Thomas-Lawford/E-Reader-MINI/firmware/src/EPD/Display_EPD_W21_SPI.c

#include "Display_EPD_W21_spi.h"

//E-paper GPIO initialization
void EPD_GPIO_Init(void)
{
	    GPIO_InitTypeDef GPIO_InitStruct = {0};

    __HAL_RCC_GPIOA_CLK_ENABLE();
    __HAL_RCC_GPIOB_CLK_ENABLE();

    // CS (PA15), output
    GPIO_InitStruct.Pin = GPIO_PIN_15;
    GPIO_InitStruct.Mode = GPIO_MODE_OUTPUT_PP;
    GPIO_InitStruct.Pull = GPIO_NOPULL;
    GPIO_InitStruct.Speed = GPIO_SPEED_FREQ_LOW;
    HAL_GPIO_Init(GPIOA, &GPIO_InitStruct);

    // MOSI (PB5), CLK (PB3), DC (PB4), RST (PB6), output
    GPIO_InitStruct.Pin = GPIO_PIN_3 | GPIO_PIN_4 | GPIO_PIN_5 | GPIO_PIN_6;
    HAL_GPIO_Init(GPIOB, &GPIO_InitStruct);

    // BUSY (PB1), input with pull-up
    GPIO_InitStruct.Pin = GPIO_PIN_1;
    GPIO_InitStruct.Mode = GPIO_MODE_INPUT;
    GPIO_InitStruct.Pull = GPIO_PULLUP;
    HAL_GPIO_Init(GPIOB, &GPIO_InitStruct); //make sure configured in cubemx
}



//SPI write byte
void SPI_Write(unsigned char value)
{
	unsigned char i;
  EPD_W21_CLK_0;
	for(i=0;i<8;i++)
	{
		if(value&0x80)
		  EPD_W21_MOSI_1 ;
		else
		  EPD_W21_MOSI_0 ;
		EPD_W21_CLK_1;
	  EPD_W21_CLK_0;
		value=value<<1;
  }
}

//SPI write command
void EPD_W21_WriteCMD(unsigned char command)
{
	EPD_W21_CS_0;
	EPD_W21_DC_0;  // D/C#   0:command  1:data
	SPI_Write(command);
	EPD_W21_CS_1;
}
//SPI write data
void EPD_W21_WriteDATA(unsigned char datas)
{
	EPD_W21_CS_0;
	EPD_W21_DC_1;  // D/C#   0:command  1:data
	SPI_Write(datas);
	EPD_W21_CS_1;
}
