Thomas-Lawford/E-Reader-MINI/firmware/src/EPD/Display_EPD_W21_spi.h

#ifndef _DISPLAY_EPD_W21_SPI_
#define _DISPLAY_EPD_W21_SPI_
#include "stm32u0xx_hal.h"


#define EPD_W21_MOSI_0	HAL_GPIO_WritePin(GPIOB, GPIO_PIN_5, GPIO_PIN_RESET)
#define EPD_W21_MOSI_1	HAL_GPIO_WritePin(GPIOB, GPIO_PIN_5, GPIO_PIN_SET)

#define EPD_W21_CLK_0	HAL_GPIO_WritePin(GPIOB, GPIO_PIN_3, GPIO_PIN_RESET)
#define EPD_W21_CLK_1	HAL_GPIO_WritePin(GPIOB, GPIO_PIN_3, GPIO_PIN_SET)

#define EPD_W21_CS_0	HAL_GPIO_WritePin(GPIOA, GPIO_PIN_15, GPIO_PIN_RESET)
#define EPD_W21_CS_1	HAL_GPIO_WritePin(GPIOA, GPIO_PIN_15, GPIO_PIN_SET)

#define EPD_W21_DC_0	HAL_GPIO_WritePin(GPIOB, GPIO_PIN_4, GPIO_PIN_RESET)
#define EPD_W21_DC_1	HAL_GPIO_WritePin(GPIOB, GPIO_PIN_4, GPIO_PIN_SET)

#define EPD_W21_RST_0	HAL_GPIO_WritePin(GPIOB, GPIO_PIN_6, GPIO_PIN_RESET)
#define EPD_W21_RST_1	HAL_GPIO_WritePin(GPIOB, GPIO_PIN_6, GPIO_PIN_SET)

#define isEPD_W21_BUSY HAL_GPIO_ReadPin(GPIOB, GPIO_PIN_1) // for solomen solutions


void SPI_Write(unsigned char value);
void EPD_W21_WriteDATA(unsigned char datas);
void EPD_W21_WriteCMD(unsigned char command);
void EPD_GPIO_Init(void);

#endif  //#ifndef _MCU_SPI_H_
