Thomas-Lawford/E-Reader-MINI/firmware/src/EPD/Display_EPD_W21.h

#ifndef _DISPLAY_EPD_W21_H_
#define _DISPLAY_EPD_W21_H_



#define EPD_WIDTH   192
#define EPD_HEIGHT  176
#define EPD_ARRAY  EPD_WIDTH*EPD_HEIGHT/8


void EPD_HW_Init_CustomLUT(void);
extern const unsigned char lut_full_update[];

//Full screen refresh display
void EPD_HW_Init(unsigned int size);
void SSD1681_LoadCustomLUT(void);
void EPD_HW_Init_180(void);
void EPD_WhiteScreen_ALL(const unsigned char *datas);
void EPD_WhiteScreen_White(void);
void EPD_WhiteScreen_Black(void);
void EPD_DeepSleep(unsigned int type);
//Partial refresh display
void EPD_SetRAMValue_BaseMap(const unsigned char * datas);
void EPD_Dis_PartAll(const unsigned char * datas);
void EPD_Dis_Part(unsigned int x_start,unsigned int y_start,const unsigned char * datas,unsigned int PART_COLUMN,unsigned int PART_LINE);
void EPD_Dis_Part_Time(unsigned int x_startA,unsigned int y_startA,const unsigned char * datasA,
	                       unsigned int x_startB,unsigned int y_startB,const unsigned char * datasB,
												 unsigned int x_startC,unsigned int y_startC,const unsigned char * datasC,
												 unsigned int x_startD,unsigned int y_startD,const unsigned char * datasD,
											   unsigned int x_startE,unsigned int y_startE,const unsigned char * datasE,
												 unsigned int PART_COLUMN,unsigned int PART_LINE
	                      );
//Fast refresh display
void EPD_HW_Init_Fast(unsigned int size);
void EPD_WhiteScreen_ALL_Fast(const unsigned char *datas);
//GUI display
void EPD_HW_Init_GUI(void);
void EPD_Display(unsigned char *Image);

#endif
