Thomas-Lawford/E-Reader-MINI/firmware/src/EPD/Ap_29demo.h

//////////////////////Bureau brush refreshes the number/////////////////////
//Digital presentation array
const unsigned char Num[10][256] = {
//0
{
0XFF,0XFF,0XFF,0XFF,0XFF,0XFF,0XFF,0XFF,0XFF,0XFF,0XFF,0XFF,0XFF,0XFF,0XFF,0XFF,
0XFF,0XFF,0XFF,0XE0,0X03,0XFF,0XFF,0XFF,0XFF,0XFF,0XFC,0X00,0X00,0X1F,0XFF,0XFF,
0XFF,0XFF,0XE0,0X00,0X00,0X03,0XFF,0XFF,0XFF,0XFF,0X80,0X00,0X00,0X00,0XFF,0XFF,
0XFF,0XFE,0X00,0X00,0X00,0X00,0X3F,0XFF,0XFF,0XFC,0X00,0X00,0X00,0X00,0X1F,0XFF,
0XFF,0XF8,0X00,0X00,0X00,0X00,0X0F,0XFF,0XFF,0XF0,0X03,0XFF,0XFF,0XE0,0X07,0XFF,
0XFF,0XE0,0X3F,0XFF,0XFF,0XFE,0X03,0XFF,0XFF,0XE0,0XFF,0XFF,0XFF,0XFF,0X83,0XFF,
0XFF,0XC1,0XFF,0XFF,0XFF,0XFF,0XC1,0XFF,0XFF,0XC7,0XFF,0XFF,0XFF,0XFF,0XF1,0XFF,
0XFF,0XC7,0XFF,0XFF,0XFF,0XFF,0XF1,0XFF,0XFF,0XCF,0XFF,0XFF,0XFF,0XFF,0XF9,0XFF,
0XFF,0XCF,0XFF,0XFF,0XFF,0XFF,0XF9,0XFF,0XFF,0XC7,0XFF,0XFF,0XFF,0XFF,0XF1,0XFF,
0XFF,0XC7,0XFF,0XFF,0XFF,0XFF,0XF1,0XFF,0XFF,0XC3,0XFF,0XFF,0XFF,0XFF,0XE1,0XFF,
0XFF,0XE0,0XFF,0XFF,0XFF,0XFF,0X83,0XFF,0XFF,0XE0,0X3F,0XFF,0XFF,0XFE,0X03,0XFF,
0XFF,0XF0,0X03,0XFF,0XFF,0XC0,0X07,0XFF,0XFF,0XF8,0X00,0X00,0X00,0X00,0X0F,0XFF,
0XFF,0XFC,0X00,0X00,0X00,0X00,0X1F,0XFF,0XFF,0XFE,0X00,0X00,0X00,0X00,0X3F,0XFF,
0XFF,0XFF,0X80,0X00,0X00,0X00,0XFF,0XFF,0XFF,0XFF,0XE0,0X00,0X00,0X03,0XFF,0XFF,
0XFF,0XFF,0XFE,0X00,0X00,0X3F,0XFF,0XFF,0XFF,0XFF,0XFF,0XFF,0XFF,0XFF,0XFF,0XFF,
0XFF,0XFF,0XFF,0XFF,0XFF,0XFF,0XFF,0XFF,0XFF,0XFF,0XFF,0XFF,0XFF,0XFF,0XFF,0XFF,
},
//1
{
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
0XFF,0XFF,0XFF,0XFF,0XFF,0XFF,0XFF,0XFF,0XFF,0XFF,0XFF,0XFF,0XE3,0XFF,0XFF,
0XFF,0XFF,0XFF,0XFF,0XFF,0XFF,0XFF,0XFF,0XFF,0XFF,0XFF,0XFF,0XFF,0XFF,0XFF,0XFF,
0XFF,0XFF,0XFF,0XFF,0XFF,0XE3,0XFF,0XFF,0XFF,0XFF,0XFF,0XFF,0XFF,0XFF,0XFF,
0XFF,0XFF,0XFF,0XFF,0XFF,0XFF,0XFF,0XFF,
};
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
